KayosMaker/CANboard_Mounts/images/overmolded_strain_relief2.png

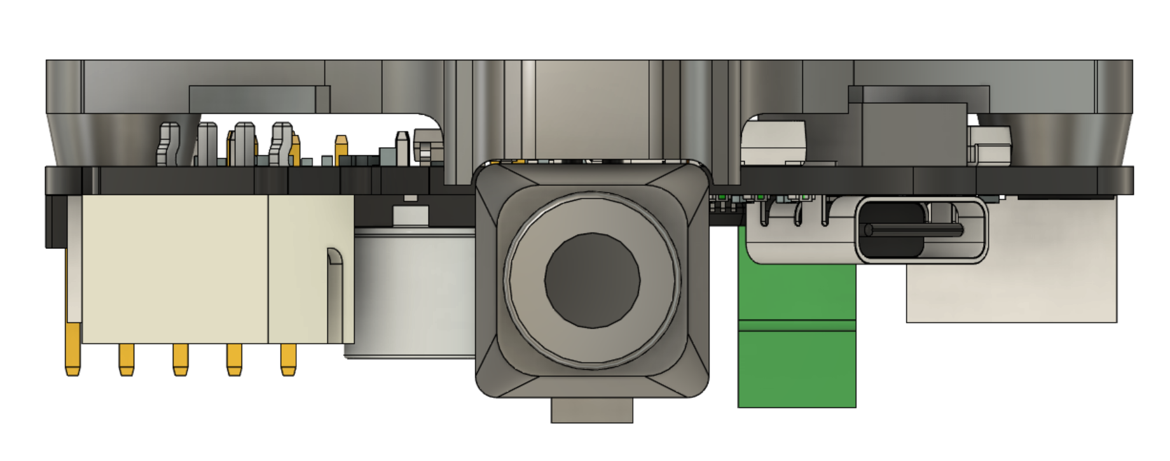
images/overmolded_strain_relief2.png
