KayosMaker/CANboard_Mounts/images/sht36_complete_rear.png

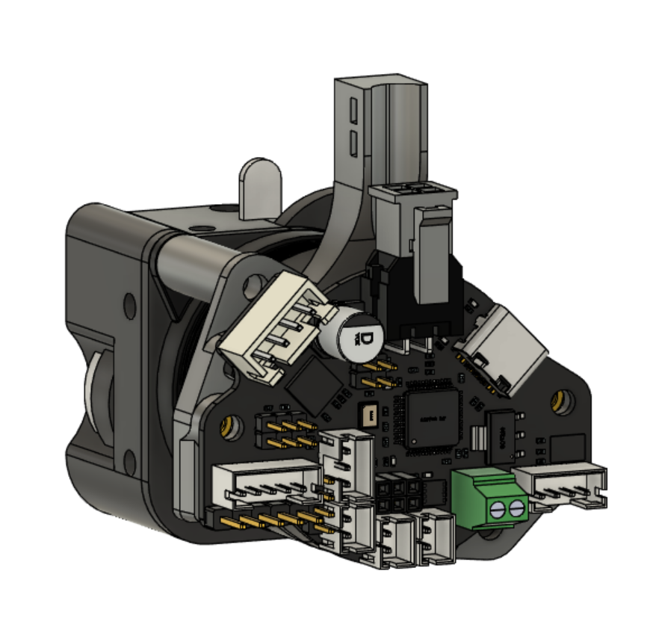
images/sht36_complete_rear.png
