KayosMaker/CANboard_Mounts/STLs/Mellow_SHT36_BTT_EBB36_1.1_1.2_Mounts/Mellow_SHT36_and_BTT_EBB36_1.1_1.2_mounts_with_strain_relief/STH-36_and_BTT_EBB36_1.1_1.2_orbiter_2.0_mounting_plate_strain_relief.stl

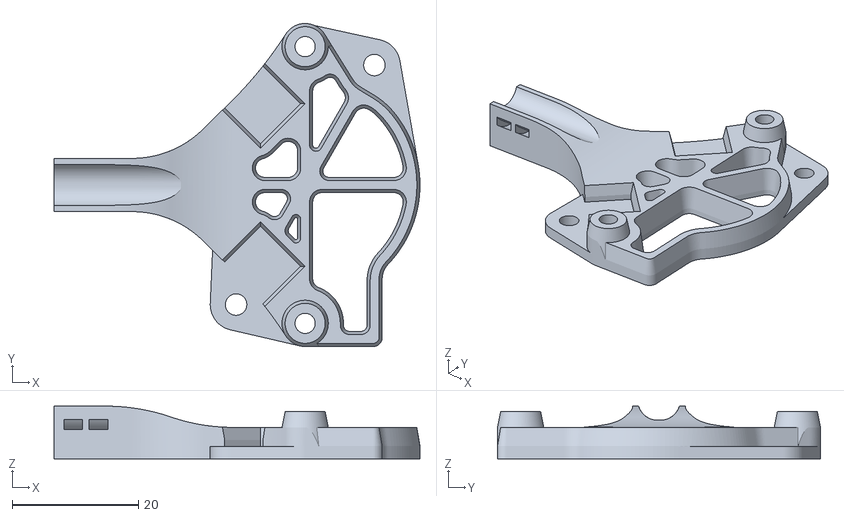
[picture p31: CAD file, 2023-08-04]
STLs/Mellow_SHT36_BTT_EBB36_1.1_1.2_Mounts/Mellow_SHT36_and_BTT_EBB36_1.1_1.2_mounts_with_strain_relief/STH-36_and_BTT_EBB36_1.1_1.2_orbiter_2.0_mounting_plate_strain_relief.stl
58.0 x 51.2 x 8.36
