KayosMaker/CANboard_Mounts/Usermods/Reapola/Galileo Mount for SHT36/CAD/sht36_galileo_rear_v4.step

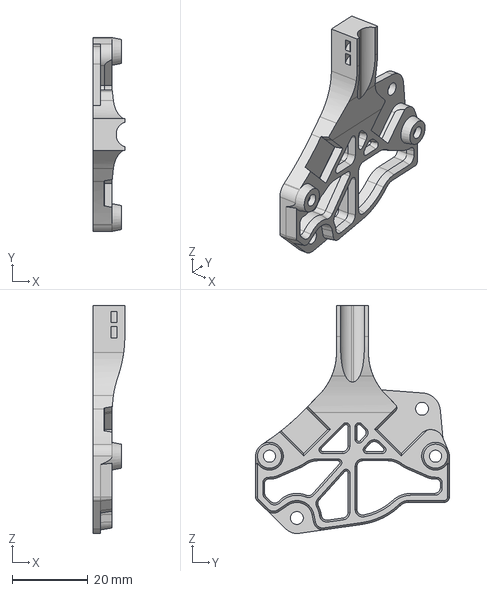
[picture p35: CAD file, 2022-07-27]
Usermods/Reapola/Galileo Mount for SHT36/CAD/sht36_galileo_rear_v4.step
8.36 x 51.2 x 60.2 mm
