KayosMaker/CANboard_Mounts/STLs/BTT_EBB36_1.0_Mounts/BTT_EBB36_1.0_mounts_plain/EBB36 1.0 orbiter 1.5 mount.stl

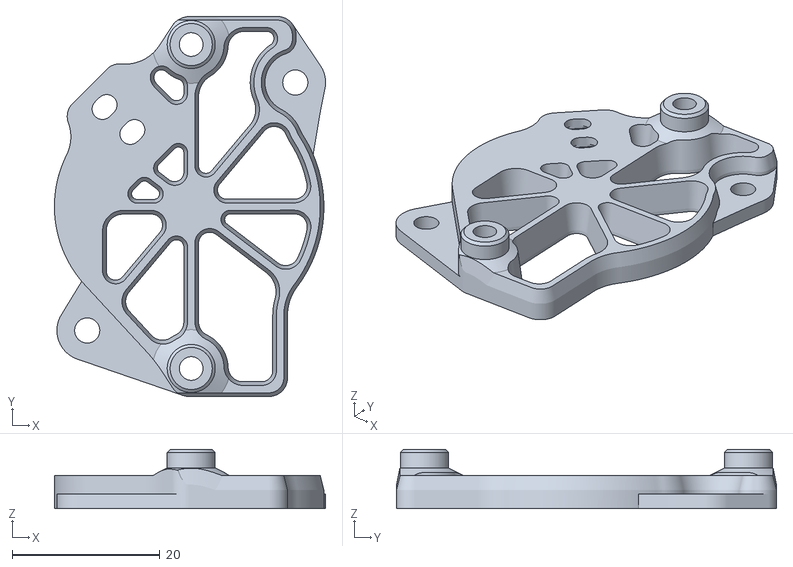
[picture p36: CAD file, 2022-05-07]
STLs/BTT_EBB36_1.0_Mounts/BTT_EBB36_1.0_mounts_plain/EBB36 1.0 orbiter 1.5 mount.stl
36.7 x 51.4 x 8.00
