KayosMaker/CANboard_Mounts/STLs/BTT_EBB36_1.0_Mounts/BTT_EBB36_1.0_mounts_with_overmold_strain_relief/EBB36 1.0 sailfin mount overmold strain relief.stl

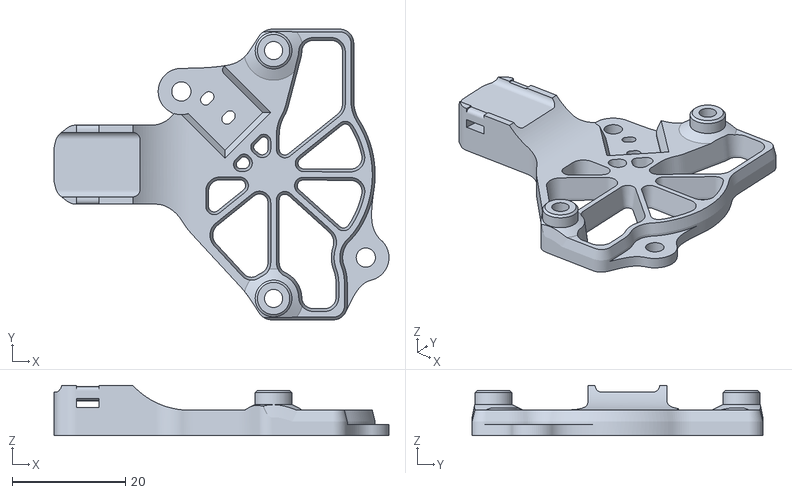
[picture p37: CAD file, 2022-05-07]
STLs/BTT_EBB36_1.0_Mounts/BTT_EBB36_1.0_mounts_with_overmold_strain_relief/EBB36 1.0 sailfin mount overmold strain relief.stl
59.2 x 51.4 x 8.86
