KayosMaker/CANboard_Mounts/STLs/BTT_EBB36_1.0_Mounts/BTT_EBB36_1.0_mounts_with_strain_relief/EBB36 1.0 orbiter 2.0 mount strain relief.stl

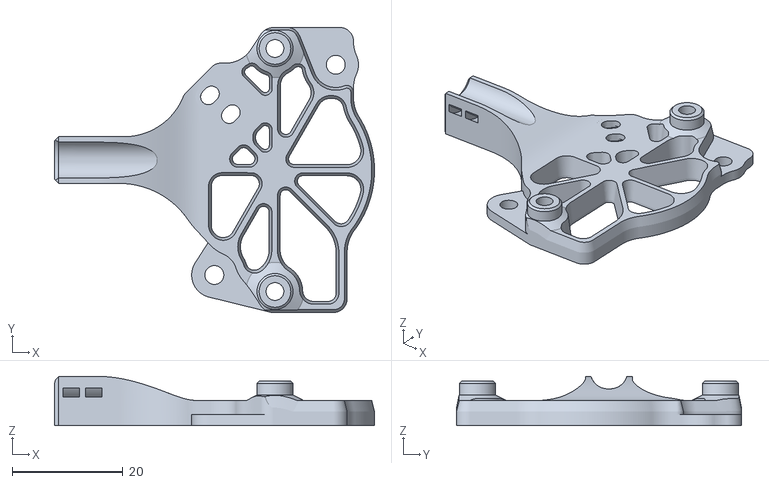
[picture p38: CAD file, 2022-05-07]
STLs/BTT_EBB36_1.0_Mounts/BTT_EBB36_1.0_mounts_with_strain_relief/EBB36 1.0 orbiter 2.0 mount strain relief.stl
57.7 x 51.4 x 8.86
