KayosMaker/CANboard_Mounts/STLs/Mellow_SHT36_BTT_EBB36_1.1_1.2_Mounts/Mellow_SHT36_and_BTT_EBB36_1.1_1.2_mounts_plain/STH-36_and_BTT_EBB36_1.1_1.2_sailfin_mounting_plate.stl

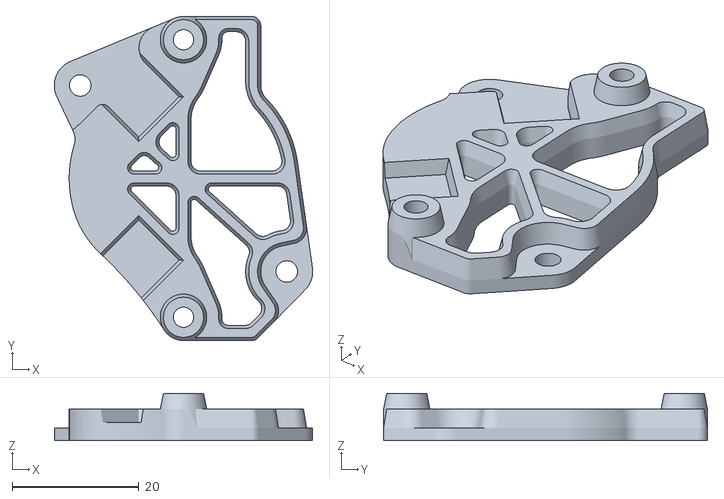
[picture p39: CAD file, 2023-08-04]
STLs/Mellow_SHT36_BTT_EBB36_1.1_1.2_Mounts/Mellow_SHT36_and_BTT_EBB36_1.1_1.2_mounts_plain/STH-36_and_BTT_EBB36_1.1_1.2_sailfin_mounting_plate.stl
40.8 x 51.2 x 7.50
