KayosMaker/CANboard_Mounts/Usermods/mk-maddin/K78l12-500R3_24-12V_mount/STL/Mellow_SHT36_BTT_EBB36_1.1_1.2_Mount/Mellow_SHT36_and_BTT_EBB36_1.1_1.2_mounts_plain/STH-36_orbiter_2.0_mounting_plate_K78l12-500R3.stl

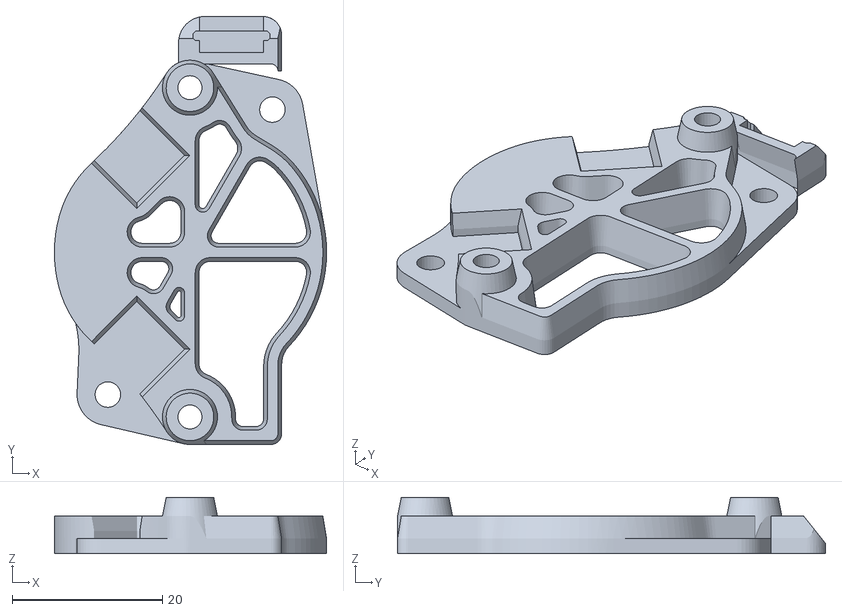
[picture p43: CAD file, 2023-10-06]
Usermods/mk-maddin/K78l12-500R3_24-12V_mount/STL/Mellow_SHT36_BTT_EBB36_1.1_1.2_Mount/Mellow_SHT36_and_BTT_EBB36_1.1_1.2_mounts_plain/STH-36_orbiter_2.0_mounting_plate_K78l12-500R3.stl
36.3 x 57.0 x 7.50
