KayosMaker/CANboard_Mounts/STLs/BTT_EBB36_1.0_Mounts/BTT_EBB36_1.0_mounts_with_overmold_strain_relief/button_x0_for_sailfin__x2_for_all_others.stl

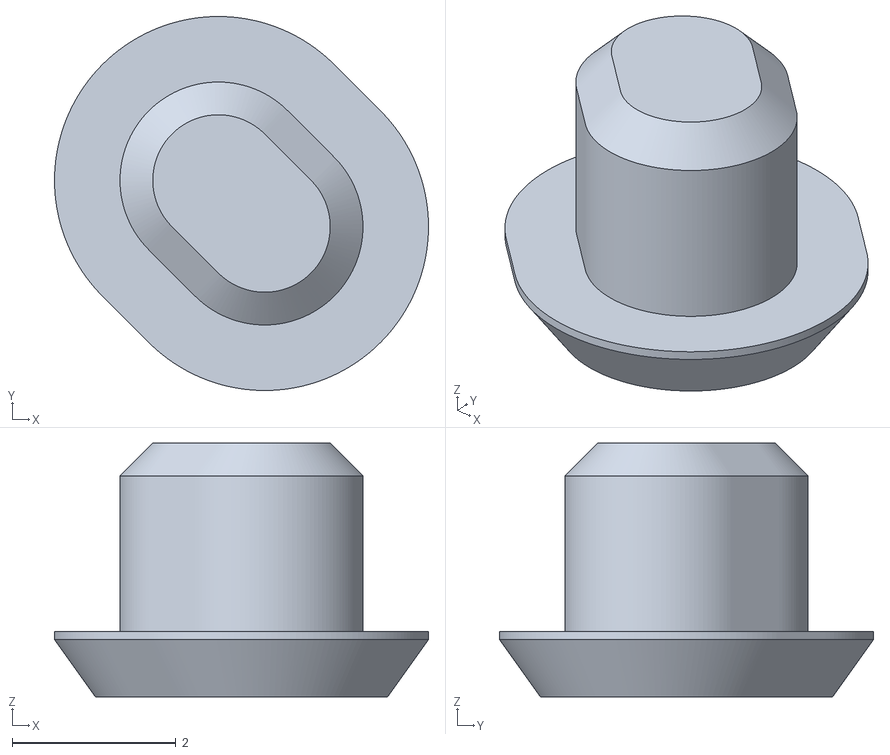
[picture p46: CAD file, 2022-05-07]
STLs/BTT_EBB36_1.0_Mounts/BTT_EBB36_1.0_mounts_with_overmold_strain_relief/button_x0_for_sailfin__x2_for_all_others.stl
4.57 x 4.57 x 3.10
