KayosMaker/CANboard_Mounts/STLs/motor_standoff_posts/19.0mm_oct_universal_spacer.stl

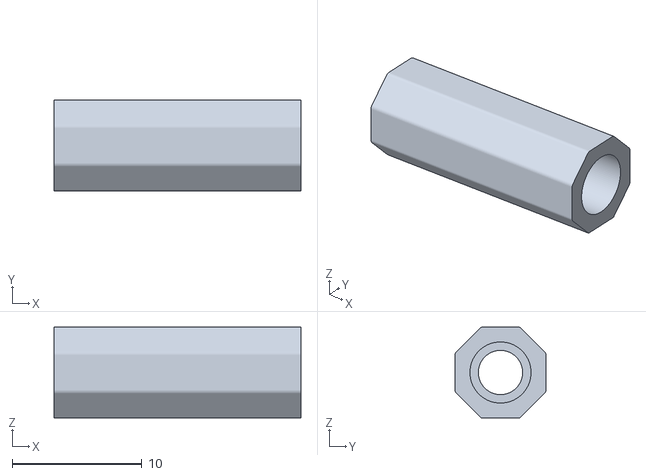
[picture p51: CAD file, 2022-04-12]
STLs/motor_standoff_posts/19.0mm_oct_universal_spacer.stl
19.0 x 7.00 x 7.00
