KayosMaker/CANboard_Mounts/Usermods/mk-maddin/K78l12-500R3_24-12V_mount/STL/Mellow_SHT36_BTT_EBB36_1.1_1.2_Mount/Mellow_SHT36_and_BTT_EBB36_1.1_1.2_mounts_with_overmold_strain_relief/SHT-36_vzhextrudort_cnc_mounting_plate_overmold_strain_K78l12-500R3.stl

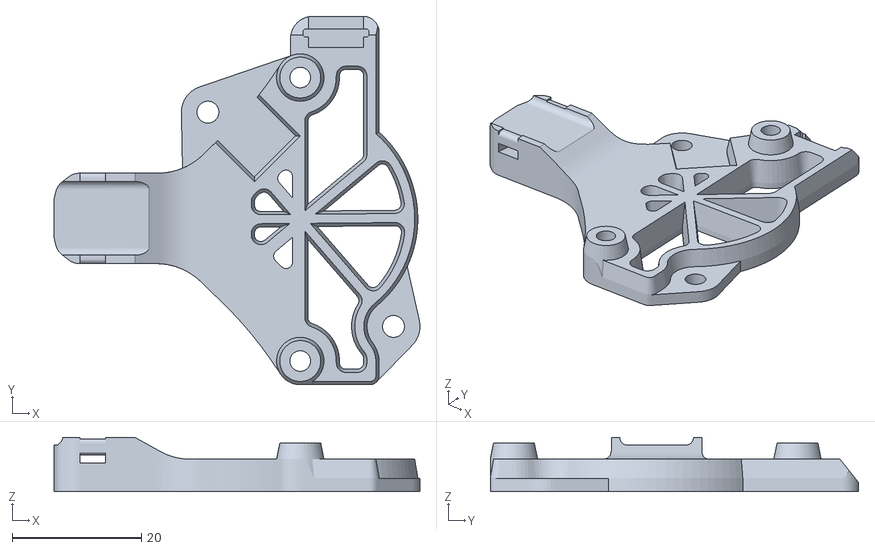
[picture p53: CAD file, 2023-10-06]
Usermods/mk-maddin/K78l12-500R3_24-12V_mount/STL/Mellow_SHT36_BTT_EBB36_1.1_1.2_Mount/Mellow_SHT36_and_BTT_EBB36_1.1_1.2_mounts_with_overmold_strain_relief/SHT-36_vzhextrudort_cnc_mounting_plate_over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
56.6 x 57.0 x 8.36
