KayosMaker/CANboard_Mounts/STLs/Mellow_SHT36_BTT_EBB36_1.1_1.2_Mounts/Mellow_SHT36_and_BTT_EBB36_1.1_1.2_mounts_plain/STH-36_and_BTT_EBB36_1.1_1.2_orbiter_1.5_mounting_plate.stl

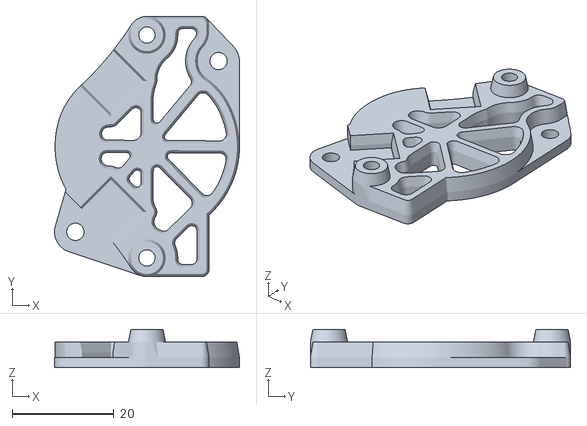
[picture p57: CAD file, 2023-08-04]
STLs/Mellow_SHT36_BTT_EBB36_1.1_1.2_Mounts/Mellow_SHT36_and_BTT_EBB36_1.1_1.2_mounts_plain/STH-36_and_BTT_EBB36_1.1_1.2_orbiter_1.5_mounting_plate.stl
36.4 x 51.2 x 7.50
