KayosMaker/CANboard_Mounts/STLs/motor_standoff_posts/18.5mm_oct_universal_spacer.stl

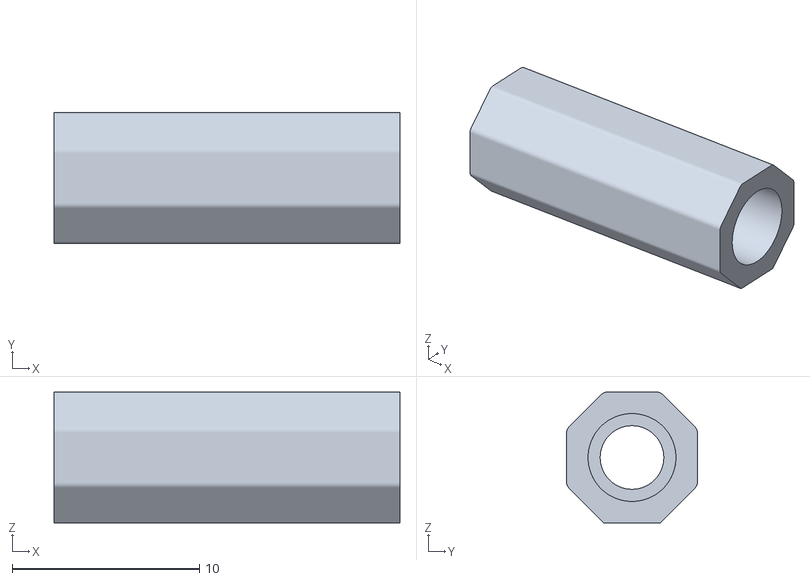
[picture p59: CAD file, 2022-04-12]
STLs/motor_standoff_posts/18.5mm_oct_universal_spacer.stl
18.5 x 7.00 x 7.00
