KayosMaker/CANboard_Mounts/Usermods/mk-maddin/K78l12-500R3_24-12V_mount/STL/Mellow_SHT36_BTT_EBB36_1.1_1.2_Mount/Mellow_SHT36_and_BTT_EBB36_1.1_1.2_mounts_with_strain_relief/STH-36_sailfin_mounting_plate_strain_relief_K78l12-500R3.stl

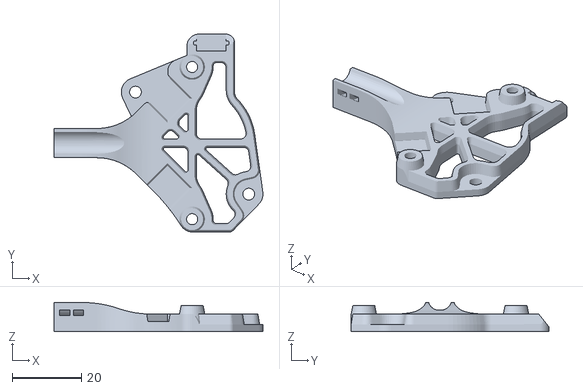
[picture p62: CAD file, 2023-10-06]
Usermods/mk-maddin/K78l12-500R3_24-12V_mount/STL/Mellow_SHT36_BTT_EBB36_1.1_1.2_Mount/Mellow_SHT36_and_BTT_EBB36_1.1_1.2_mounts_with_strain_relief/STH-36_sailfin_mounting_plate_strain_relief_K78l12-5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
60.2 x 57.0 x 8.36
