KayosMaker/CANboard_Mounts/STLs/motor_standoff_posts/16.0mm_round_universal_spacer.stl

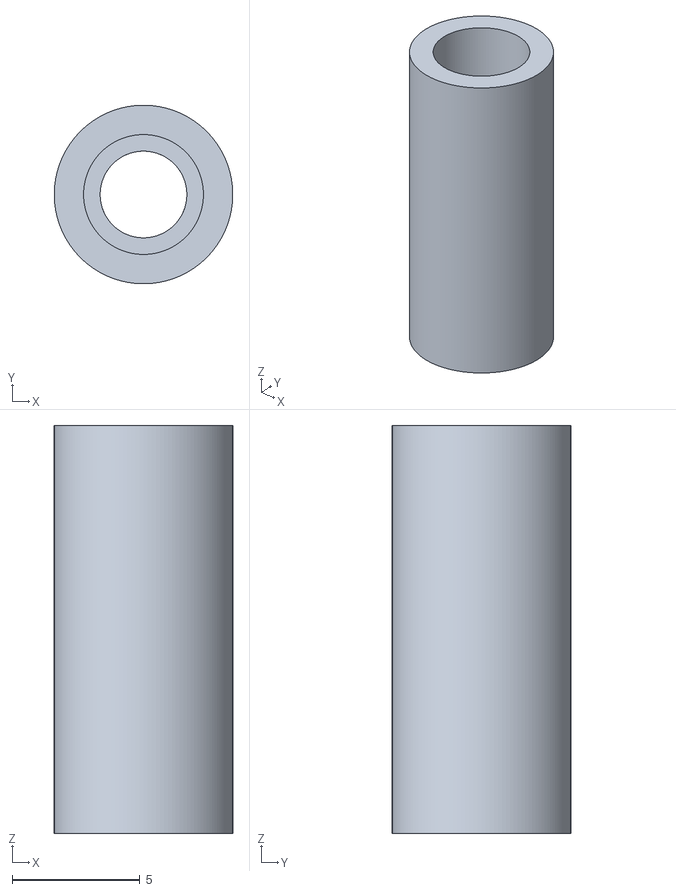
[picture p73: CAD file, 2022-04-12]
STLs/motor_standoff_posts/16.0mm_round_universal_spacer.stl
7.00 x 7.00 x 16.0
