KayosMaker/CANboard_Mounts/Usermods/mk-maddin/K78l12-500R3_24-12V_mount/STL/Mellow_SHT36_BTT_EBB36_1.1_1.2_Mount/Mellow_SHT36_and_BTT_EBB36_1.1_1.2_mounts_with_strain_relief/SHT-36_sherpa_micro_mounting_plate_strain_relief_K78l12-500R3.stl

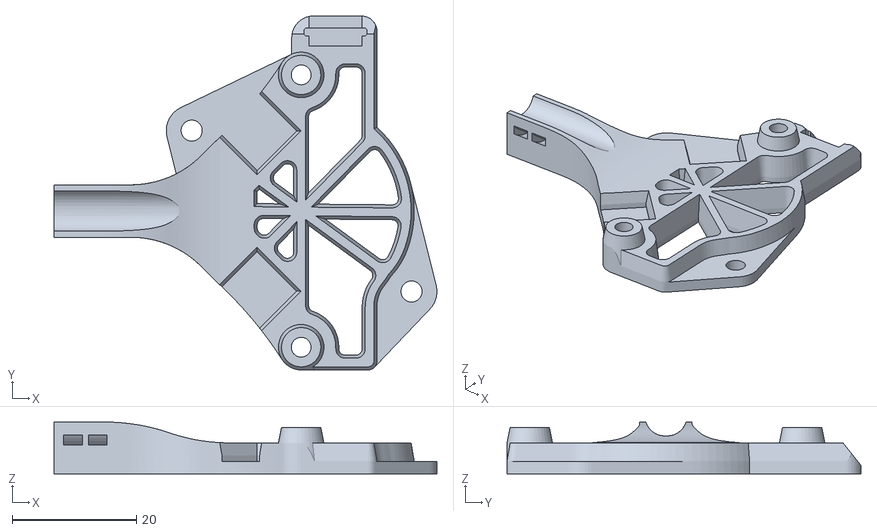
[picture p76: CAD file, 2023-10-06]
Usermods/mk-maddin/K78l12-500R3_24-12V_mount/STL/Mellow_SHT36_BTT_EBB36_1.1_1.2_Mount/Mellow_SHT36_and_BTT_EBB36_1.1_1.2_mounts_with_strain_relief/SHT-36_sherpa_micro_mounting_plate_strain_relief_K78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
61.6 x 57.0 x 8.36
