KayosMaker/CANboard_Mounts/STLs/Mellow_SHT36_BTT_EBB36_1.1_1.2_Mounts/Mellow_SHT36_and_BTT_EBB36_1.1_1.2_mounts_plain/SHT-36_and_BTT_EBB36_1.1_1.2_sherpa_micro_mounting_plate.stl

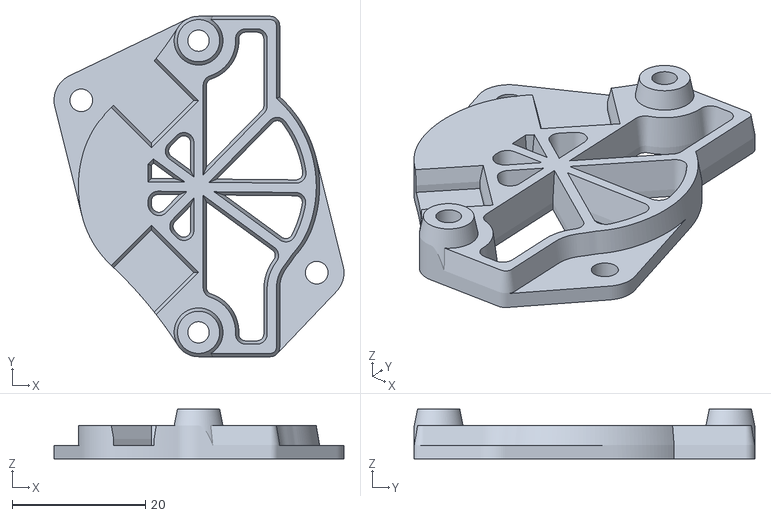
[picture p77: CAD file, 2023-08-04]
STLs/Mellow_SHT36_BTT_EBB36_1.1_1.2_Mounts/Mellow_SHT36_and_BTT_EBB36_1.1_1.2_mounts_plain/SHT-36_and_BTT_EBB36_1.1_1.2_sherpa_micro_mounting_plate.stl
43.6 x 51.2 x 7.50
