KayosMaker/CANboard_Mounts/STLs/Mellow_SHT36_BTT_EBB36_1.1_1.2_Mounts/Mellow_SHT36_and_BTT_EBB36_1.1_1.2_mounts_plain/STH-36_and_BTT_EBB36_1.1_1.2_sherpa_mini_mounting_plate.stl

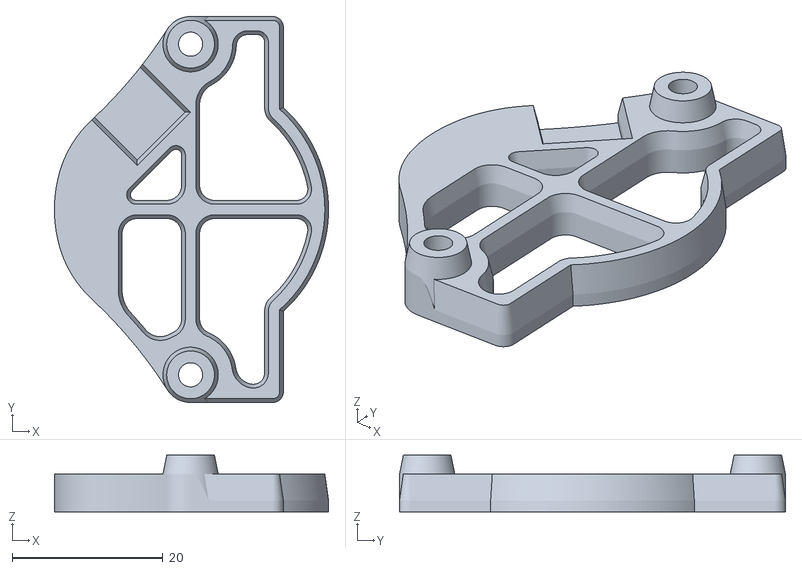
[picture p84: CAD file, 2022-04-09]
STLs/Mellow_SHT36_BTT_EBB36_1.1_1.2_Mounts/Mellow_SHT36_and_BTT_EBB36_1.1_1.2_mounts_plain/STH-36_and_BTT_EBB36_1.1_1.2_sherpa_mini_mounting_plate.stl
36.3 x 51.2 x 7.50
