KayosMaker/CANboard_Mounts/STLs/Mellow_SHT36_BTT_EBB36_1.1_1.2_Mounts/Mellow_SHT36_and_BTT_EBB36_1.1_1.2_mounts_with_overmold_strain_relief/STH-36_and_BTT_EBB36_1.1__sherpa_mini_mounting_plate_overmold_strain.stl

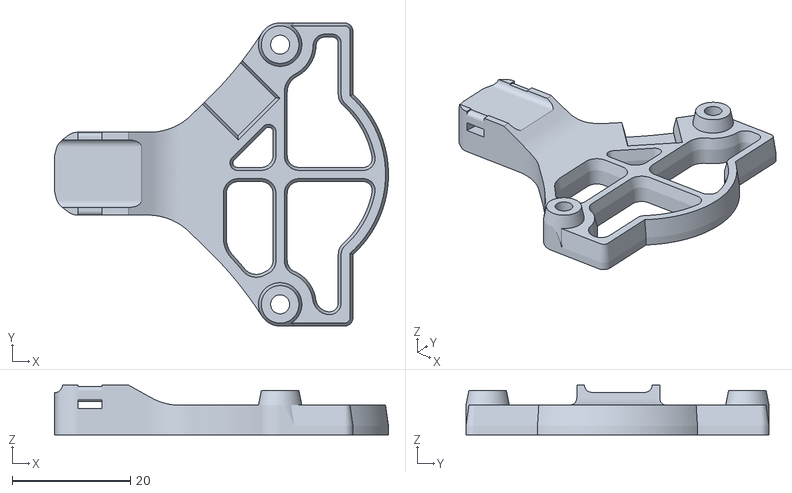
[picture p85: CAD file, 2022-04-18]
STLs/Mellow_SHT36_BTT_EBB36_1.1_1.2_Mounts/Mellow_SHT36_and_BTT_EBB36_1.1_1.2_mounts_with_overmold_strain_relief/STH-36_and_BTT_EBB36_1.1__sherpa_mini_mounting_plate_overmold_strain.stl
56.4 x 51.2 x 8.36
