KayosMaker/CANboard_Mounts/STLs/Mellow_SHT36_BTT_EBB36_1.1_1.2_Mounts/Mellow_SHT36_and_BTT_EBB36_1.1_1.2_mounts_with_strain_relief/STH-36_and_BTT_EBB36_1.1_1.2_sherpa_mini_mounting_plate_strain_relief.stl

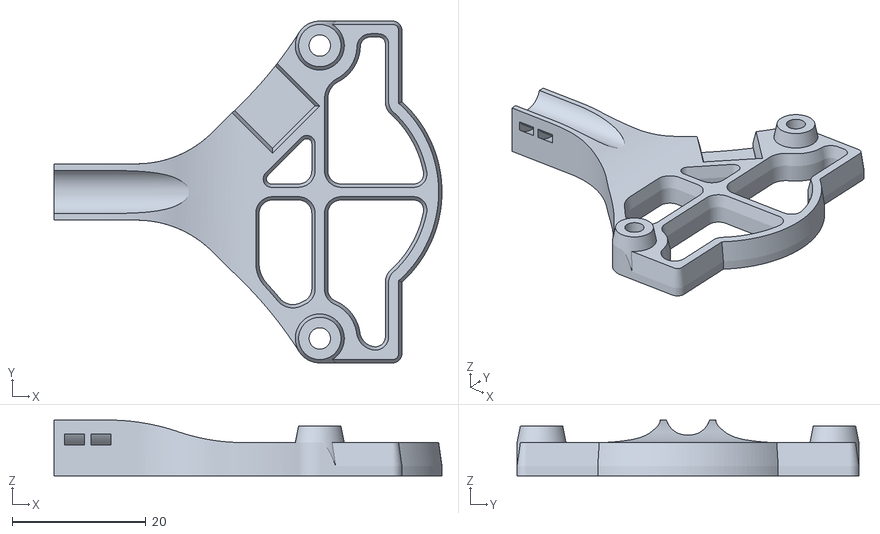
[picture p86: CAD file, 2022-04-09]
STLs/Mellow_SHT36_BTT_EBB36_1.1_1.2_Mounts/Mellow_SHT36_and_BTT_EBB36_1.1_1.2_mounts_with_strain_relief/STH-36_and_BTT_EBB36_1.1_1.2_sherpa_mini_mounting_plate_strain_relief.stl
58.1 x 51.2 x 8.36
