KayosMaker/CANboard_Mounts/STLs/motor_standoff_posts/16.5mm_teardrop_universal_spacer.stl

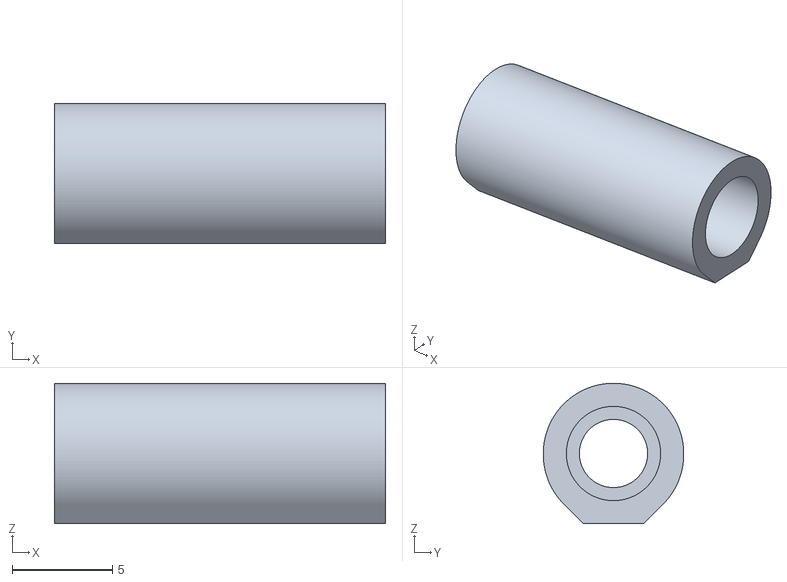
[picture p87: CAD file, 2022-04-12]
STLs/motor_standoff_posts/16.5mm_teardrop_universal_spacer.stl
16.5 x 7.00 x 7.00
