KayosMaker/CANboard_Mounts/STLs/motor_standoff_posts/17.5mm_teardrop_universal_spacer.stl

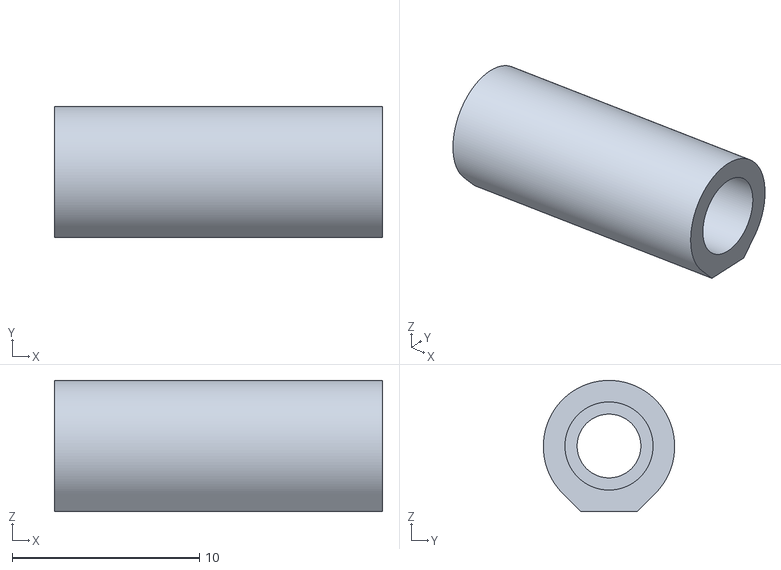
[picture p95: CAD file, 2022-04-12]
STLs/motor_standoff_posts/17.5mm_teardrop_universal_spacer.stl
17.5 x 7.00 x 7.00
