KayosMaker/CANboard_Mounts/STLs/motor_standoff_posts/14.5mm_round_universal_spacer.stl

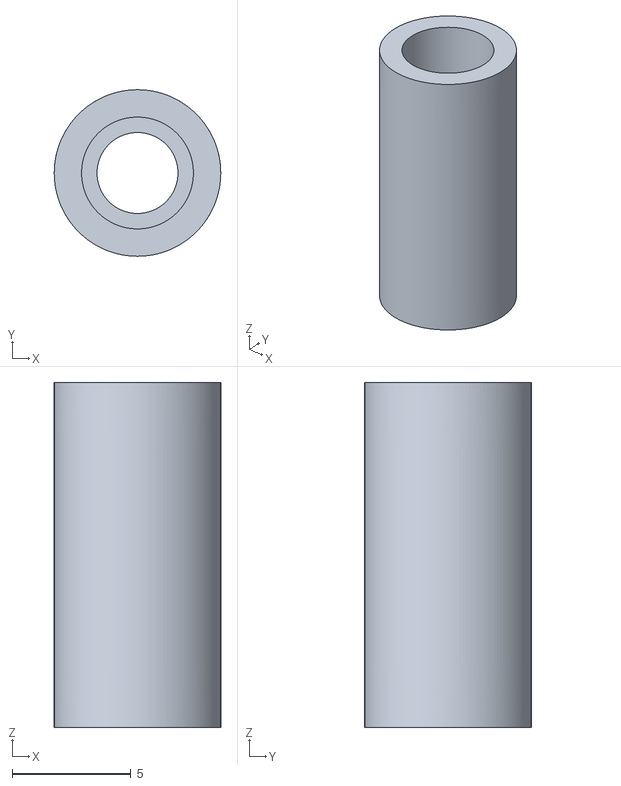
[picture p98: CAD file, 2022-04-12]
STLs/motor_standoff_posts/14.5mm_round_universal_spacer.stl
7.00 x 7.00 x 14.5
