KayosMaker/CANboard_Mounts/STLs/motor_standoff_posts/16.0mm_teardrop_universal_spacer.stl

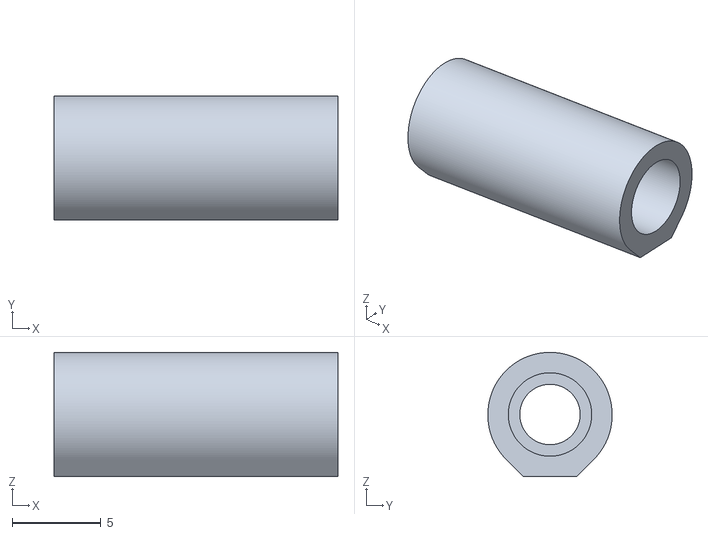
[picture p101: CAD file, 2022-04-12]
STLs/motor_standoff_posts/16.0mm_teardrop_universal_spacer.stl
16.0 x 7.00 x 7.00
