KayosMaker/CANboard_Mounts/STLs/motor_standoff_posts/16.5mm_oct_universal_spacer.stl

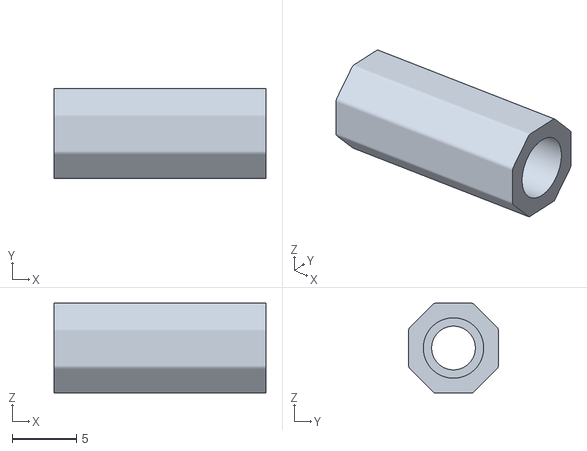
[picture p103: CAD file, 2022-04-12]
STLs/motor_standoff_posts/16.5mm_oct_universal_spacer.stl
16.5 x 7.00 x 7.00
