KayosMaker/CANboard_Mounts/STLs/motor_standoff_posts/18.0mm_round_universal_spacer.stl

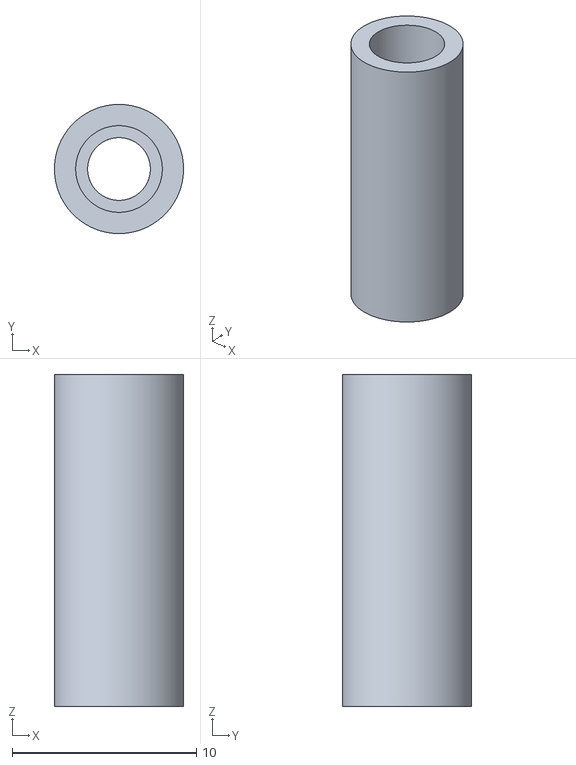
[picture p106: CAD file, 2022-04-12]
STLs/motor_standoff_posts/18.0mm_round_universal_spacer.stl
7.00 x 7.00 x 18.0
