KayosMaker/CANboard_Mounts/STLs/motor_standoff_posts/15.0mm_teardrop_universal_spacer.stl

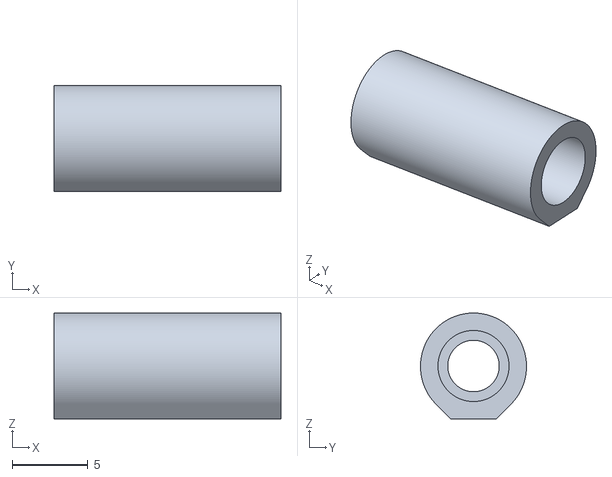
[picture p108: CAD file, 2022-04-12]
STLs/motor_standoff_posts/15.0mm_teardrop_universal_spacer.stl
15.0 x 7.00 x 7.00
